swharden/USB-Counter/graphics/2019-07-25.jpg

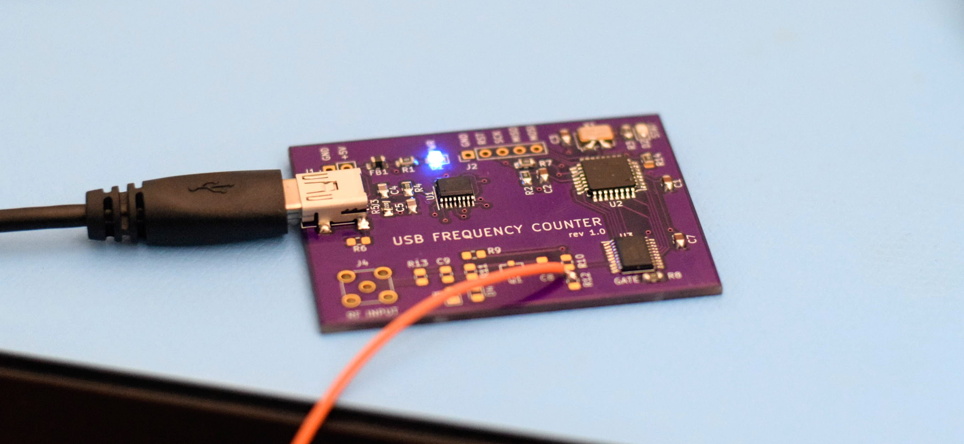
graphics/2019-07-25.jpg
