swharden/USB-Counter/graphics/2019-07-26-bodge.JPG

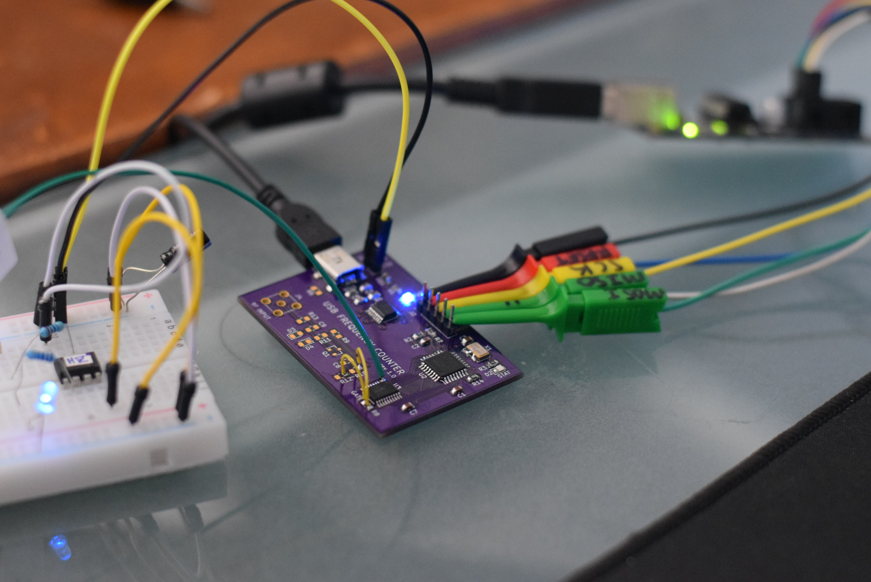
graphics/2019-07-26-bodge.JPG
