swharden/USB-Counter/graphics/2019-07-26-output.png

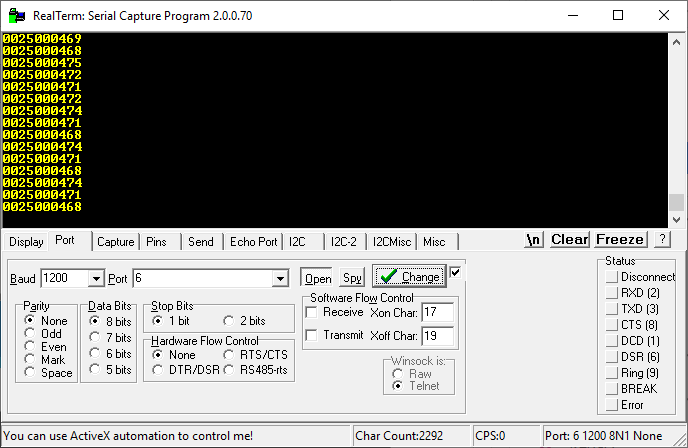
graphics/2019-07-26-output.png
