swharden/USB-Counter/builds/2.2/pcb.png

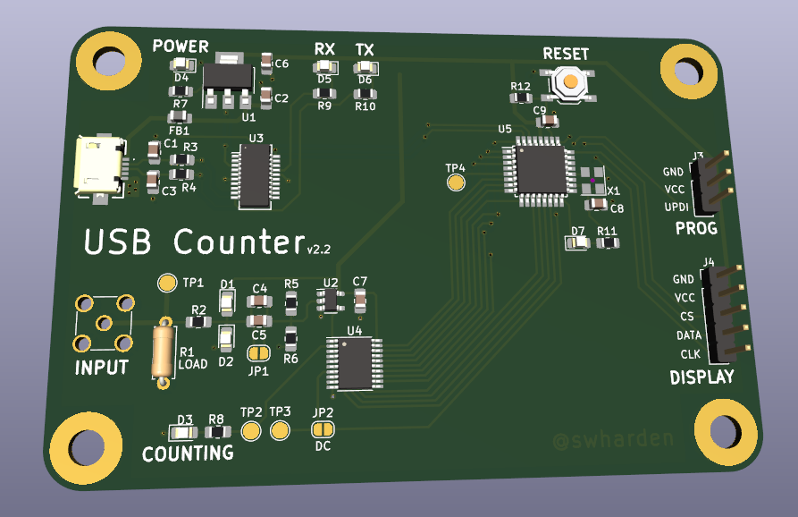
builds/2.2/pcb.png
