swharden/USB-Counter/builds/1.1/LTSpice/Draft3.asc

C1: cap; .1µ
C2: cap; .1µ
C3: cap; .1µ
D1: diode; 1N4148
D2: diode; 1N4148
Q1: npn; 2N3904
R1: res; 10k
R2: res; 1k
R3: res; 50
R4: res; 10k
R5: res; 10k
V1: voltage; 3.3
V2: voltage; SINE(0 5 1MEG)
Named nets: 0
.tran 0 .001 .000990
