swharden/USB-Counter/builds/1.0/LTSpice/Draft1.asc

C1: cap; 120p
C2: cap; 120p
C3: cap; 120p
C4: cap; 7p
C5: cap; .1µ
C6: cap; .1µ
Q1: npn; 2N3904
Q2: npn; 2N3904
R1: res; 220
R2: res; 30
R3: res; 10k
R4: res; 10k
R5: res; 10k
R6: res; 1k
R7: res; 50
R10: res; 50
V1: voltage; 5V
V2: voltage; SINE(0 1 10meg)
Named nets: 0
.tran 0 .001 .000999
TRY THIS CONFIG: R3, R6
250 mW
