swharden/USB-Counter/builds/1.0/LTSpice/Draft2.asc

C1: cap; .1µ
C2: cap; .1µ
C3: cap; .1µ
D1: diode; 1N4148
D2: diode; 1N4148
Q1: npn; 2N2222
R1: res; 10k
R2: res; 1k
R3: res; 1k
R4: res; 10k
R5: res; 10k
V1: voltage; 5
V2: voltage; SINE(0 .5 1MEG)
Named nets: 0
.tran 0 .001 .000990
