swharden/USB-Counter/builds/3.0/software/NumberSpeaker.h

#ifndef NumberSpeaker_h
#define NumberSpeaker_h

#include <avr/pgmspace.h>

const uint8_t* AUDIO_P1; // address currently being played
const uint8_t* AUDIO_P2; // last address in the array being played

#define IsPlaying() AUDIO_P1 < AUDIO_P2

uint8_t GetNextAudioLevel() {
	if (AUDIO_P1 < AUDIO_P2){
		return pgm_read_byte(AUDIO_P1++);
		} else {
		return 128;
	}
}


const uint8_t AUDIO_SAMPLES_0[] PROGMEM = {
	128, 128, 129, 129, 129, 130, 130, 130, 130, 130, 129, 129, 129, 128, 127, 127, 126, 125, 124, 124,
	123, 123, 123, 123, 124, 124, 125, 126, 126, 127, 127, 128, 130, 132, 131, 130, 129, 129, 127, 123,
	120, 119, 118, 116, 115, 115, 117, 118, 120, 122, 125, 129, 133, 135, 138, 141, 143, 144, 143, 143,
	142, 139, 137, 134, 132, 130, 129, 127, 127, 127, 126, 126, 126, 126, 125, 124, 123, 121, 119, 116,
	115, 113, 112, 110, 110, 109, 109, 107, 107, 109, 110, 113, 116, 120, 124, 129, 133, 137, 140, 143,
	145, 147, 148, 149, 148, 147, 144, 143, 140, 137, 133, 131, 130, 128, 127, 128, 130, 131, 129, 129,
	127, 126, 124, 122, 120, 117, 115, 113, 111, 109, 107, 106, 105, 106, 106, 109, 112, 116, 121, 125,
	129, 134, 137, 140, 141, 143, 144, 144, 144, 144, 143, 142, 140, 137, 134, 131, 129, 127, 127, 126,
	125, 124, 120, 118, 116, 113, 111, 109, 109, 107, 106, 106, 108, 110, 111, 113, 117, 121, 124, 126,
	130, 134, 138, 141, 144, 146, 149, 150, 149, 145, 143, 142, 139, 137, 135, 135, 134, 132, 132, 133,
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
	30,  45,  71,  79,  63,  49,  40,  59,  64,  71,  59,  49,  56,  87, 150, 219, 220, 196, 153, 136,
	142, 155, 177, 163, 165, 179, 217, 243, 225, 184, 141, 127, 141, 149, 150, 135, 129, 136, 152, 154,
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
};

void speak_digit(uint8_t digit) {
	switch (digit) {
		
		case 0:
		AUDIO_P1 = AUDIO_SAMPLES_0;
		AUDIO_P2 = AUDIO_P1 + sizeof(AUDIO_SAMPLES_0);
		break;
		
		case 1:
		AUDIO_P1 = AUDIO_SAMPLES_1;
		AUDIO_P2 = AUDIO_P1 + sizeof(AUDIO_SAMPLES_1);
		break;
		
		case 2:
		AUDIO_P1 = AUDIO_SAMPLES_2;
		AUDIO_P2 = AUDIO_P1 + sizeof(AUDIO_SAMPLES_2);
		break;
		
		case 3:
		AUDIO_P1 = AUDIO_SAMPLES_3;
		AUDIO_P2 = AUDIO_P1 + sizeof(AUDIO_SAMPLES_3);
		break;
		
		case 4:
		AUDIO_P1 = AUDIO_SAMPLES_4;
		AUDIO_P2 = AUDIO_P1 + sizeof(AUDIO_SAMPLES_4);
		break;
		
		case 5:
		AUDIO_P1 = AUDIO_SAMPLES_5;
		AUDIO_P2 = AUDIO_P1 + sizeof(AUDIO_SAMPLES_5);
		break;
		
		case 6:
		AUDIO_P1 = AUDIO_SAMPLES_6;
		AUDIO_P2 = AUDIO_P1 + sizeof(AUDIO_SAMPLES_6);
		break;
		
		case 7:
		AUDIO_P1 = AUDIO_SAMPLES_7;
		AUDIO_P2 = AUDIO_P1 + sizeof(AUDIO_SAMPLES_7);
		break;
		
		case 8:
		AUDIO_P1 = AUDIO_SAMPLES_8;
		AUDIO_P2 = AUDIO_P1 + sizeof(AUDIO_SAMPLES_8);
		break;
		
		case 9:
		AUDIO_P1 = AUDIO_SAMPLES_9;
		AUDIO_P2 = AUDIO_P1 + sizeof(AUDIO_SAMPLES_9);
		break;
		
		default:
		AUDIO_P1 = AUDIO_SAMPLES_POINT;
		AUDIO_P2 = AUDIO_P1 + sizeof(AUDIO_SAMPLES_POINT);
		break;
	}
	
	while(IsPlaying()){}
}

void speak_point(){
	speak_digit(11);
}

void speak_digits(uint32_t value){
	
	if (value == 0){
		speak_digit(0);
		while(IsPlaying()){}
		return;
	}
	
	uint32_t divisor = 1000000000;
	uint8_t real_numbers_seen = 0;
	while(divisor > 0){
		uint8_t digit = value/divisor;
		
		if (digit > 0){
			real_numbers_seen = 1;
		}
		
		if (real_numbers_seen){
			speak_digit(digit);
			while(IsPlaying()){}
		}

		value = value - (digit*divisor);
		divisor /= 10;
	}
}

void speak_mhz(uint32_t frequency, uint8_t decimals){
	
	uint32_t divisor = 1000000000;
	uint8_t real_numbers_seen = 0;
	
	uint32_t exit_after_divisor = 100000;
	
	uint8_t said_something = 0;
	
	while (decimals--){
		exit_after_divisor/=10;
	}
	
	while(divisor > 0){
		uint8_t digit = frequency/divisor;
		
		if (digit > 0){
			real_numbers_seen = 1;
		}
		
		if (real_numbers_seen || (divisor<10000000)){
			speak_digit(digit);
			said_something = 1;
			if (divisor==1000000){
				speak_point();
			}
		}
		
		frequency = frequency - (digit*divisor);
		divisor /= 10;
		
		if (divisor == exit_after_divisor){
			break;
		}
	}
	
	if (!said_something){
		speak_digit(0);
	}
}

#endif
